kipp7/landslide-monitoring-v2/docs/integrations/mqtt/README.md

---
title: README
type: note
permalink: landslide-monitoring-v2-mainline/docs/integrations/mqtt/readme
---

# integrations/mqtt/

该目录描述设备接入的对接契约（MQTT Broker、Topic、Payload、鉴权/ACL）。

索引：
- `docs/integrations/mqtt/device-identity-and-auth.md`
- `docs/integrations/mqtt/mqtt-topics-and-envelope.md`

机器可读（Schema）：

- TelemetryEnvelope：`docs/integrations/mqtt/schemas/telemetry-envelope.v1.schema.json`
- DeviceCommand：`docs/integrations/mqtt/schemas/device-command.v1.schema.json`
- DeviceCommandAck：`docs/integrations/mqtt/schemas/device-command-ack.v1.schema.json`
- PresenceEvent：`docs/integrations/mqtt/schemas/presence-event.v1.schema.json`
