kipp7/landslide-monitoring-v2/docs/integrations/mqtt/schemas/README.md

---
title: README
type: note
permalink: landslide-monitoring-v2-mainline/docs/integrations/mqtt/schemas/readme
---

# integrations/mqtt/schemas/

本目录存放 MQTT 消息体的 JSON Schema（机器可读契约）。

索引：

- TelemetryEnvelope v1：`docs/integrations/mqtt/schemas/telemetry-envelope.v1.schema.json`
- DeviceCommand v1：`docs/integrations/mqtt/schemas/device-command.v1.schema.json`
- DeviceCommandAck v1：`docs/integrations/mqtt/schemas/device-command-ack.v1.schema.json`
- PresenceEvent v1：`docs/integrations/mqtt/schemas/presence-event.v1.schema.json`

配套示例（用于脚本校验/联调对齐）：

- `docs/integrations/mqtt/examples/README.md`
