kipp7/landslide-monitoring-v2/docs/integrations/rules/examples/README.md

---
title: README
type: note
permalink: landslide-monitoring-v2-mainline/docs/integrations/rules/examples/readme
---

# Rules DSL 示例（与 JSON Schema 对齐）

本目录存放 Rule DSL 的**机器可验证**示例。目标是：

- DSL 规范不是“口头约定”，而是可以被脚本校验的契约
- 支持“多规则 + 多传感器组合”，并为算法/AI 模块预留接口

示例文件：

- `rule-single-sensor-threshold.v1.json`
- `rule-multi-sensor-combo.v1.json`
- `rule-metric-window.v1.json`
- `rule-algo-predict.v1.json`
