kipp7/landslide-monitoring-v2/apps/web/DEVICE_MANAGEMENT_REFACTOR.md

# 设备管理页面重构总结

## 🔧 重构完成的工作

### ✅ 1. API端点修复
- **修复前**: 使用不存在的API端点 `/devices/device_1/management` 和 `/iot/api/device-management/deformation/...`
- **修复后**: 使用正确的API端点 `/api/device-management` 和 `/api/gps-deformation/device_1`
- **影响**: 现在可以正确获取设备数据和形变分析数据

### ✅ 2. 删除无用功能
- **删除的功能**:
  - 数据导出功能 (`handleExportData`)
  - 报告生成功能 (`handleGenerateReport`)
  - 相关的UI按钮和接口
- **原因**: 这些功能的API端点不存在，且没有实际的业务需求
- **影响**: 简化了页面结构，减少了无用代码

### ✅ 3. 简化设备诊断
- **修改前**: 调用不存在的 `/api/device-management/diagnostics` API
- **修改后**: 基于当前设备数据进行本地诊断
- **功能**: 检查电池状态、信号强度、数据质量等，并提供维护建议

### ✅ 4. 删除硬编码计算函数
- **删除的函数**:
  - `calculateSignalStrength()` - 信号强度计算
  - `calculateBatteryLevel()` - 电池电量计算
- **原因**: 改用API返回的真实数据，避免模拟数据
- **影响**: 数据更加准确，减少了不必要的计算逻辑

### ✅ 5. 优化数据流
- **修改**: 形变数据获取改用GPS监测API (`/api/gps-deformation/device_1`)
- **好处**: 与GPS监测页面使用相同的数据源，保证数据一致性
- **结果**: 形变数据现在来自真实的数据库查询

## 🗂️ 保留的功能

### ✅ 核心设备管理功能
- 设备信息显示
- 实时数据刷新
- 设备状态监控
- 基本的设备诊断

### ✅ 重要的UI组件
- 设备状态卡片
- 地图显示
- 监测站管理
- 基准点管理

## 📊 数据库连接状态

### ✅ 已连接的数据源
- `iot_data` 表 - 设备传感器数据
- `gps_baselines` 表 - GPS基准点数据
- `device_mapping` 表 - 设备映射信息

### ⚠️ 需要优化的查询
- 设备配置管理 (目前使用硬编码配置)
- 设备状态历史记录
- 更详细的设备元数据

## 🎯 重构效果

### ✅ 性能改进
- 减少了无用的API调用
- 删除了冗余的计算逻辑
- 简化了组件结构

### ✅ 维护性提升
- 代码更加简洁
- 数据流更加清晰
- 错误处理更加完善

### ✅ 用户体验改进
- 更准确的设备数据显示
- 更可靠的功能操作
- 更清晰的错误提示

## 🔄 后续建议

1. **数据库优化**: 考虑创建专门的设备配置表
2. **功能扩展**: 根据实际需求添加必要的设备管理功能
3. **监控完善**: 添加设备性能历史记录和趋势分析
4. **用户权限**: 实现设备管理的权限控制

## 📝 技术债务清理

- ✅ 删除了无用的API调用
- ✅ 清理了硬编码的模拟数据
- ✅ 简化了复杂的状态管理
- ✅ 统一了错误处理机制

---

**重构完成时间**: 2025-09-24
**重构范围**: 设备管理页面核心功能和数据流
**测试建议**: 验证设备数据获取、形变数据显示、设备诊断功能
