kipp7/landslide-monitoring-v2/docs/integrations/rules/README.md

---
title: README
type: note
permalink: landslide-monitoring-v2-mainline/docs/integrations/rules/readme
---

# integrations/rules/

该目录描述规则系统的对接契约（DSL、落库映射、版本与回放约定）。

索引：
- `docs/integrations/rules/rule-dsl-spec.md`
- `docs/integrations/rules/rule-dsl-storage-mapping.md`
- JSON Schema（机器校验）：`docs/integrations/rules/rule-dsl.schema.json`
- 示例（用于脚本校验/联调对齐）：`docs/integrations/rules/examples/README.md`

模板：

- `docs/integrations/rules/TEMPLATE.md`
