kipp7/landslide-monitoring-v2/docs/integrations/storage/README.md

---
title: README
type: note
permalink: landslide-monitoring-v2-mainline/docs/integrations/storage/readme
---

# integrations/storage/

该目录描述存储层契约：

- PostgreSQL：元数据/规则/告警/权限（强一致）
- ClickHouse：遥测时序与聚合（高吞吐）

索引：
- `docs/integrations/storage/overview.md`
- `docs/integrations/storage/postgres/`
- `docs/integrations/storage/clickhouse/`
