kipp7/landslide-monitoring-v2/docs/zh-CN/PROJECT_SCOPE.md

# 项目范围

这个仓库作为山体滑坡监测 V2 的公开源码树维护。当前 `main` 分支包含正在维护的桌面客户端、云端后端、RK3568 边缘网关服务、RK2206 现场固件包、载板硬件交付资料、打包脚本和公开文档。

## 当前维护范围

- `apps/desktop-ui/` - React + Vite 监测操作界面。
- `apps/windows-shell/` - WPF + WebView2 Windows 宿主和安装器资源。
- `services/` - 云端 API、遥测、告警、预测和命令处理服务。
- `infra/compose/` - 单机后端基础设施与应用部署。
- `edge/rk3568-gateway/` - RK3568 边缘服务和部署模板。
- `firmware/rk2206-xl01/` - RK2206 XL01 现场节点固件包。
- `hardware/carrier-board/` - 载板设计和打板交付资料。
- `packages/` 和 `libs/` - 边缘与后端服务共用的 TypeScript 包。
- `scripts/desktop/` - 桌面端开发、打包和验证脚本。
- `docs/` - 公开架构、发布、系统、维护和中英文文档。
- `.github/` - CI、Issue 模板、Pull Request 模板和依赖自动化配置。

## 仓库内容

公开仓库包含：

- 当前维护的桌面端、后端、边缘服务和固件应用源码。
- 公开示例和部署模板。
- 可集成进兼容 vendor 构建树的固件包文件。
- 载板设计和打板交付文件。
- 构建、lint、打包和验证脚本。
- 公开文档、Issue 模板和 Pull Request 模板。

以下内容不属于当前公开树：

- 移动端应用和 Web Dashboard 应用代码。
- 供应商 SDK 全量目录。
- 生成发布产物和本地构建输出。
- 凭据、私有端点、设备口令和本地环境文件。
- 点位特定配置、本地日志和运行状态。

## 维护规则

新增模块应补充 README、本地验证命令，并在可行时纳入 CI。未列入当前维护范围的内容，应通过明确的公开路径重新引入后，再视为受支持模块。
